Spritetm/esp32c3-doom-bauble/case/images/8a0a2fa01a11a490eb8f598237e40b69.png

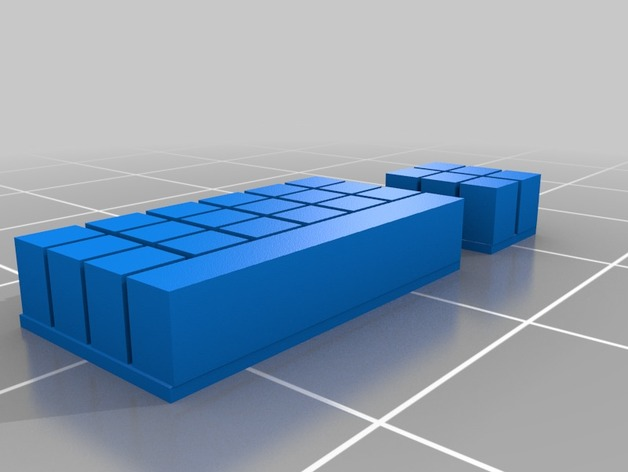
case/images/8a0a2fa01a11a490eb8f598237e40b69.png
