Spritetm/esp32c3-doom-bauble/case/images/58c1f62a23a4da21758beb00cb33d7fe.png

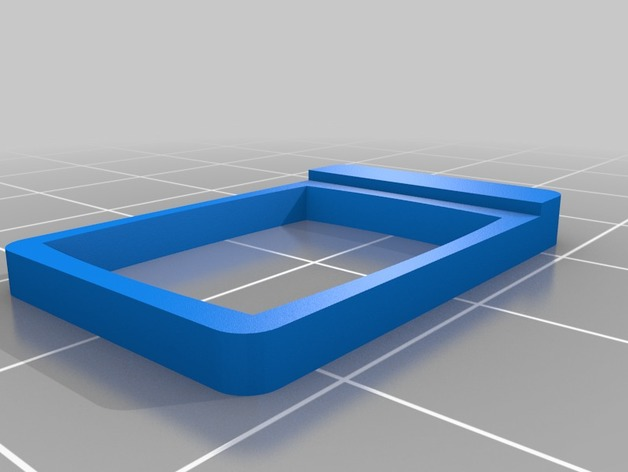
case/images/58c1f62a23a4da21758beb00cb33d7fe.png
