Spritetm/esp32c3-doom-bauble/case/images/657a22aeada5b2b08f759854bf49b2c7.png

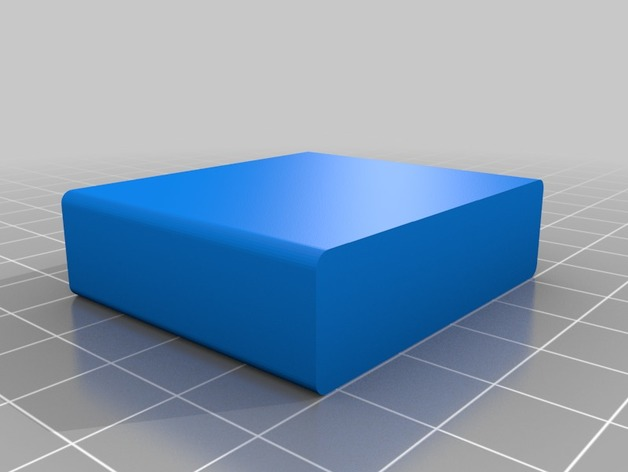
case/images/657a22aeada5b2b08f759854bf49b2c7.png
