Spritetm/esp32c3-doom-bauble/case/images/e2cab330a377aed4025e782568884b1f.png

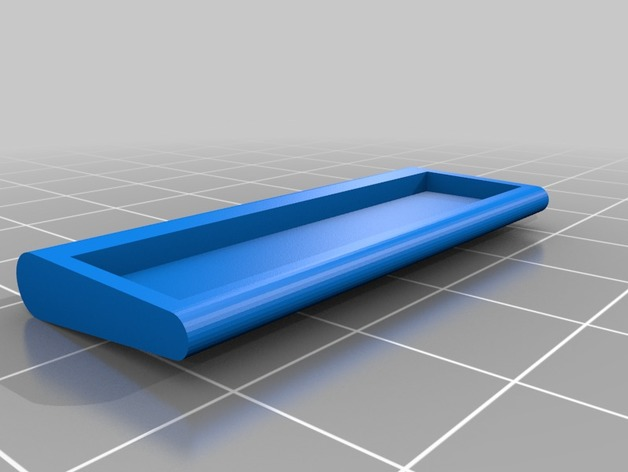
case/images/e2cab330a377aed4025e782568884b1f.png
