Spritetm/esp32c3-doom-bauble/case/images/pc3.jpg

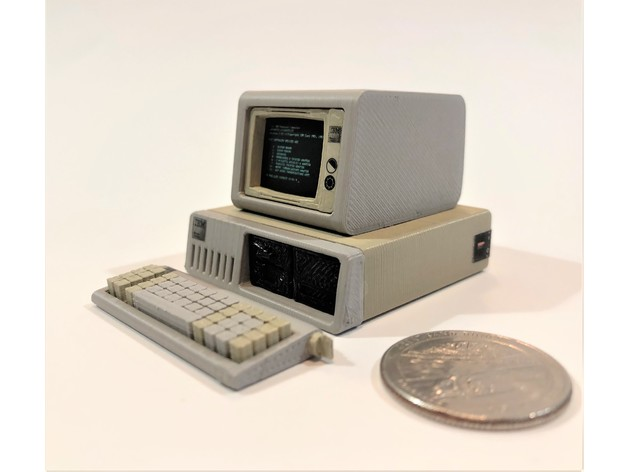
case/images/pc3.jpg
