Spritetm/esp32c3-doom-bauble/esp32c3-doom/main/s_sound.c

/* Emacs style mode select   -*- C++ -*-
 *-----------------------------------------------------------------------------
 *
 *
 *  PrBoom: a Doom port merged with LxDoom and LSDLDoom
 *  based on BOOM, a modified and improved DOOM engine
 *  Copyright (C) 1999 by
 *  id Software, Chi Hoang, Lee Killough, Jim Flynn, Rand Phares, Ty Halderman
 *  Copyright (C) 1999-2000 by
 *  Jess Haas, Nicolas Kalkhof, Colin Phipps, Florian Schulze
 *  Copyright 2005, 2006 by
 *  Florian Schulze, Colin Phipps, Neil Stevens, Andrey Budko
 *
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
 * DESCRIPTION:  Platform-independent sound code
 *
 *-----------------------------------------------------------------------------*/

// killough 3/7/98: modified to allow arbitrary listeners in spy mode
// killough 5/2/98: reindented, removed useless code, beautified

#ifdef HAVE_CONFIG_H
#include "config.h"
#endif

#include "doomstat.h"
#include "s_sound.h"
#include "i_sound.h"
#include "i_system.h"
#include "d_main.h"
#include "r_main.h"
#include "m_random.h"
#include "w_wad.h"
#include "lprintf.h"

#include "global_data.h"

// when to clip out sounds
// Does not fit the large outdoor areas.
#define S_CLIPPING_DIST (1200<<FRACBITS)

// Distance tp origin when sounds should be maxed out.
// This should relate to movement clipping resolution
// (see BLOCKMAP handling).
// Originally: (200*0x10000).

#define S_CLOSE_DIST (160<<FRACBITS)
#define S_ATTENUATOR ((S_CLIPPING_DIST-S_CLOSE_DIST)>>FRACBITS)

// Adjustable by menu.
#define NORM_PRIORITY 64
#define NORM_SEP      128

#define S_STEREO_SWING		(96*0x10000)



// number of channels available
static const unsigned int numChannels = 8;

//
// Internals.
//

void S_StopChannel(int cnum);

int S_AdjustSoundParams(mobj_t *listener, mobj_t *source, int *vol, int *sep);

static int S_getChannel(void *origin, const sfxinfo_t *sfxinfo, int is_pickup);

// Initializes sound stuff, including volume
// Sets channels, SFX and music volume,
//  allocates channel buffer, sets S_sfx lookup.
//

void S_Init(int sfxVolume, int musicVolume)
{
    //jff 1/22/98 skip sound init if sound not enabled
    if (!nosfxparm)
    {
        int i;

        lprintf(LO_CONFIRM, "S_Init: default sfx volume %d", sfxVolume);

        S_SetSfxVolume(sfxVolume);

        // Allocating the internal channels for mixing
        // (the maximum numer of sounds rendered
        // simultaneously) within zone memory.
        // CPhipps - calloc
        _g->channels =
                (channel_t *) calloc(numChannels,sizeof(channel_t));
    }

    // CPhipps - music init reformatted
    if (!nomusicparm) {
        S_SetMusicVolume(musicVolume);

        // no sounds are playing, and they are not mus_paused
        _g->mus_paused = 0;
    }
}

void S_Stop(void)
{
    unsigned int cnum;

    //jff 1/22/98 skip sound init if sound not enabled
    if (!nosfxparm)
        for (cnum=0 ; cnum<numChannels ; cnum++)
            if (_g->channels[cnum].sfxinfo)
                S_StopChannel(cnum);
}

//
// Per level startup code.
// Kills playing sounds at start of level,
//  determines music if any, changes music.
//
void S_Start(void)
{
    int mnum;

    // kill all playing sounds at start of level
    //  (trust me - a good idea)

    S_Stop();

    //jff 1/22/98 return if music is not enabled
    if (nomusicparm)
        return;

    // start new music for the level
    _g->mus_paused = 0;

    if (_g->idmusnum!=-1)
        mnum = _g->idmusnum; //jff 3/17/98 reload IDMUS music if not -1
    else
        if (_g->gamemode == commercial)
            mnum = mus_runnin + _g->gamemap - 1;
        else
        {
            static const int spmus[] =     // Song - Who? - Where?
            {
                    mus_e3m4,     // American     e4m1
                    mus_e3m2,     // Romero       e4m2
                    mus_e3m3,     // Shawn        e4m3
                    mus_e1m5,     // American     e4m4
                    mus_e2m7,     // Tim  e4m5
                    mus_e2m4,     // Romero       e4m6
                    mus_e2m6,     // J.Anderson   e4m7 CHIRON.WAD
                    mus_e2m5,     // Shawn        e4m8
                    mus_e1m9      // Tim          e4m9
        };

            if (_g->gameepisode < 4)
                mnum = mus_e1m1 + (_g->gameepisode-1)*9 + _g->gamemap-1;
            else
                mnum = spmus[_g->gamemap-1];
        }
    S_ChangeMusic(mnum, true);
}

void S_StartSoundAtVolume(mobj_t *origin, int sfx_id, int volume)
{
    int priority, cnum, is_pickup;
    const sfxinfo_t *sfx;

    int sep = NORM_SEP;

    //jff 1/22/98 return if sound is not enabled
    if (nosfxparm)
        return;

    is_pickup = sfx_id & PICKUP_SOUND || sfx_id == sfx_oof || (sfx_id == sfx_noway); // killough 4/25/98
    sfx_id &= ~PICKUP_SOUND;

    // check for bogus sound #
    if (sfx_id < 1 || sfx_id > NUMSFX)
        I_Error("S_StartSoundAtVolume: Bad sfx #: %d", sfx_id);

    sfx = &S_sfx[sfx_id];

    // Initialize sound parameters
    if (sfx->link)
    {
        priority = sfx->priority;
        volume += sfx->volume;

        if (volume < 1)
            return;

        if (volume > _g->snd_SfxVolume)
            volume = _g->snd_SfxVolume;
    }
    else
    {
        priority = NORM_PRIORITY;
    }

    // Check to see if it is audible, modify the params
    // killough 3/7/98, 4/25/98: code rearranged slightly

    if (!origin || origin == _g->player.mo)
    {
        volume *= 8;
    }
    else
        if (!S_AdjustSoundParams(_g->player.mo, origin, &volume, &sep))
            return;

    // kill old sound
    for (cnum=0 ; cnum<numChannels ; cnum++)
        if (_g->channels[cnum].sfxinfo && _g->channels[cnum].origin == origin &&
                (_g->channels[cnum].is_pickup == is_pickup))
        {
            S_StopChannel(cnum);
            break;
        }

    // try to find a channel
    cnum = S_getChannel(origin, sfx, is_pickup);

    if (cnum<0)
        return;

    int h = I_StartSound(sfx_id, cnum, volume, sep);
    if (h != -1)
    {
        _g->channels[cnum].handle = h;
        _g->channels[cnum].tickend = (_g->gametic + sfx->ticks);
    }

}

void S_StartSound(mobj_t *origin, int sfx_id)
{
    S_StartSoundAtVolume(origin, sfx_id, _g->snd_SfxVolume);
}

void S_StartSound2(degenmobj_t* origin, int sfx_id)
{
    //Look at this mess.

    //Originally, the degenmobj_t had
    //a thinker_t at the start of the struct
    //so that it could be passed around and
    //cast to a mobj_t* in the sound code
    //for non-mobj sound makers like doors.

    //This also meant that each and every sector_t
    //struct has 24 bytes wasted. I can't afford
    //to waste memory like that so we have a seperate
    //function for these cases which cobbles toget a temp
    //mobj_t-like struct to pass to the sound code.


    struct fake_mobj
    {
        thinker_t ununsed;
        degenmobj_t origin;
    } fm;

    fm.origin.x = origin->x;
    fm.origin.y = origin->y;

    S_StartSoundAtVolume((mobj_t*) &fm, sfx_id, _g->snd_SfxVolume);
}

void S_StopSound(void *origin)
{
    int cnum;

    //jff 1/22/98 return if sound is not enabled
    if (nosfxparm)
        return;

    for (cnum=0 ; cnum<numChannels ; cnum++)
        if (_g->channels[cnum].sfxinfo && _g->channels[cnum].origin == origin)
        {
            S_StopChannel(cnum);
            break;
        }
}


//
// Stop and resume music, during game PAUSE.
//
void S_PauseSound(void)
{
    //jff 1/22/98 return if music is not enabled
    if (nomusicparm)
        return;

    if (_g->mus_playing && !_g->mus_paused)
    {
        I_PauseSong(0);
        _g->mus_paused = true;
    }
}

void S_ResumeSound(void)
{
    //jff 1/22/98 return if music is not enabled
    if (nomusicparm)
        return;

    if (_g->mus_playing && _g->mus_paused)
    {
        I_ResumeSong(0);
        _g->mus_paused = false;
    }
}

static boolean S_SoundIsPlaying(int cnum)
{
    const channel_t* channel = &_g->channels[cnum];

    if(channel->sfxinfo)
    {
        int ticknow = _g->gametic;

        return (channel->tickend < ticknow);
    }

    return false;
}

//
// Updates music & sounds
//
void S_UpdateSounds(void* listener_p)
{
	mobj_t *listener = (mobj_t*) listener_p;
	int cnum;
    int sep = NORM_SEP;
	
	//jff 1/22/98 return if sound is not enabled
	if (nosfxparm)
		return;
	
	for (cnum=0 ; cnum<numChannels ; cnum++)
	{
        const sfxinfo_t *sfx;
        channel_t *c = &_g->channels[cnum];
		
		if ((sfx = c->sfxinfo))
		{
            if (S_SoundIsPlaying(c->handle))
			{
				// initialize parameters
                int volume = _g->snd_SfxVolume;

				if (sfx->link)
				{
					volume += sfx->volume;
					
					if (volume < 1)
					{
						S_StopChannel(cnum);
						continue;
					}
					else
					{
                        if (volume > _g->snd_SfxVolume)
                            volume = _g->snd_SfxVolume;

					}
				}
			}
			else   // if channel is allocated but sound has stopped, free it
				S_StopChannel(cnum);
		}
	}
}

void S_SetMusicVolume(int volume)
{
    //jff 1/22/98 return if music is not enabled
    if (nomusicparm)
        return;
    if (volume < 0 || volume > 15)
        I_Error("S_SetMusicVolume: Attempt to set music volume at %d", volume);
    I_SetMusicVolume(volume);
    _g->snd_MusicVolume = volume;
}



void S_SetSfxVolume(int volume)
{
    //jff 1/22/98 return if sound is not enabled
    if (nosfxparm)
        return;
    if (volume < 0 || volume > 127)
        I_Error("S_SetSfxVolume: Attempt to set sfx volume at %d", volume);
    _g->snd_SfxVolume = volume;
}



// Starts some music with the music id found in sounds.h.
//
void S_StartMusic(int m_id)
{
    //jff 1/22/98 return if music is not enabled
    if (nomusicparm)
        return;
    S_ChangeMusic(m_id, false);
}

void S_ChangeMusic(int musicnum, int looping)
{
    //jff 1/22/98 return if music is not enabled
    if (nomusicparm)
        return;

    if (musicnum <= mus_None || musicnum >= NUMMUSIC)
        I_Error("S_ChangeMusic: Bad music number %d", musicnum);

    if (_g->mus_playing == musicnum)
        return;

    // shutdown old music
    S_StopMusic();

    // play it
    I_PlaySong(musicnum, looping);

    _g->mus_playing = musicnum;
}


void S_StopMusic(void)
{
    //jff 1/22/98 return if music is not enabled
    if (nomusicparm)
        return;

    if (_g->mus_playing)
    {
        if (_g->mus_paused)
            I_ResumeSong(0);

        I_StopSong(0);

        _g->mus_playing = 0;
    }
}



void S_StopChannel(int cnum)
{
    int i;
    channel_t *c = &_g->channels[cnum];

    //jff 1/22/98 return if sound is not enabled
    if (nosfxparm)
        return;

    if (c->sfxinfo)
    {
        // check to see
        //  if other channels are playing the sound
        for (i=0 ; i<numChannels ; i++)
            if (cnum != i && c->sfxinfo == _g->channels[i].sfxinfo)
                break;

        // degrade usefulness of sound data
        c->sfxinfo = 0;
        c->tickend = 0;
    }
}

//
// Changes volume, stereo-separation, and pitch variables
//  from the norm of a sound effect to be played.
// If the sound is not audible, returns a 0.
// Otherwise, modifies parameters and returns 1.
//

int S_AdjustSoundParams(mobj_t *listener, mobj_t *source, int *vol, int *sep)
{
	fixed_t adx, ady,approx_dist;

	//jff 1/22/98 return if sound is not enabled
	if (nosfxparm)
		return 0;

	
	if (!listener)
		return 0;

	// calculate the distance to sound origin
	// and clip it if necessary
	adx = D_abs(listener->x - source->x);
	ady = D_abs(listener->y - source->y);

	// From _GG1_ p.428. Appox. eucledian distance fast.
	approx_dist = adx + ady - ((adx < ady ? adx : ady)>>1);

	if (!approx_dist)  // killough 11/98: handle zero-distance as special case
	{
        *vol = _g->snd_SfxVolume;
		return *vol > 0;
	}
	
	if (approx_dist > S_CLIPPING_DIST)
		return 0;
	

    // angle of source to listener
    angle_t angle = R_PointToAngle2(listener->x, listener->y, source->x, source->y);

    if (angle <= listener->angle)
        angle += 0xffffffff;

    angle -= listener->angle;
    angle >>= ANGLETOFINESHIFT;

    // stereo separation
    *sep = 128 - (FixedMul(S_STEREO_SWING,finesine[angle])>>FRACBITS);


	// volume calculation
	if (approx_dist < S_CLOSE_DIST)
        *vol = _g->snd_SfxVolume*8;
	else
		// distance effect
        *vol = (_g->snd_SfxVolume * ((S_CLIPPING_DIST-approx_dist)>>FRACBITS) * 8) / S_ATTENUATOR;
	
	return (*vol > 0);
}

//
// S_getChannel :
//   If none available, return -1.  Otherwise channel #.
//
// killough 4/25/98: made static, added is_pickup argument

static int S_getChannel(void *origin, const sfxinfo_t *sfxinfo, int is_pickup)
{
    // channel number to use
    int cnum;
    channel_t *c;

    //jff 1/22/98 return if sound is not enabled
    if (nosfxparm)
        return -1;

    // Find an open channel
    for (cnum=0; cnum<numChannels && _g->channels[cnum].sfxinfo; cnum++)
        if (origin && _g->channels[cnum].origin == origin &&
                _g->channels[cnum].is_pickup == is_pickup)
        {
            S_StopChannel(cnum);
            break;
        }

    // None available
    if (cnum == numChannels)
    {      // Look for lower priority
        for (cnum=0 ; cnum<numChannels ; cnum++)
            if (_g->channels[cnum].sfxinfo->priority >= sfxinfo->priority)
                break;
        if (cnum == numChannels)
            return -1;                  // No lower priority.  Sorry, Charlie.
        else
            S_StopChannel(cnum);        // Otherwise, kick out lower priority.
    }

    c = &_g->channels[cnum];              // channel is decided to be cnum.
    c->sfxinfo = sfxinfo;
    c->origin = origin;
    c->is_pickup = is_pickup;         // killough 4/25/98
    return cnum;
}
