Spritetm/esp32c3-doom-bauble/esp32c3-doom/main/g_game.h

/* Emacs style mode select   -*- C++ -*-
 *-----------------------------------------------------------------------------
 *
 *
 *  PrBoom: a Doom port merged with LxDoom and LSDLDoom
 *  based on BOOM, a modified and improved DOOM engine
 *  Copyright (C) 1999 by
 *  id Software, Chi Hoang, Lee Killough, Jim Flynn, Rand Phares, Ty Halderman
 *  Copyright (C) 1999-2000 by
 *  Jess Haas, Nicolas Kalkhof, Colin Phipps, Florian Schulze
 *  Copyright 2005, 2006 by
 *  Florian Schulze, Colin Phipps, Neil Stevens, Andrey Budko
 *
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
 * DESCRIPTION: Main game control interface.
 *-----------------------------------------------------------------------------*/

#ifndef __G_GAME__
#define __G_GAME__

#include "doomdef.h"
#include "d_event.h"
#include "d_ticcmd.h"

//
// GAME
//

// killough 5/2/98: number of bytes reserved for saving options
#define GAME_OPTION_SIZE 64

boolean G_Responder(event_t *ev);
boolean G_CheckDemoStatus(void);
void G_InitNew(skill_t skill, int episode, int map);
void G_DeferedInitNew(skill_t skill, int episode, int map);
void G_DeferedPlayDemo(const char *demo); // CPhipps - const
void G_LoadGame(int slot, boolean is_command); // killough 5/15/98
void G_ForcedLoadGame(void);           // killough 5/15/98: forced loadgames
void G_DoLoadGame(void);
void G_SaveGame(int slot, const char *description); // Called by M_Responder.
void G_ExitLevel(void);
void G_SecretExitLevel(void);
void G_WorldDone(void);
void G_EndGame(void); /* cph - make m_menu.c call a G_* function for this */
void G_Ticker(void);
void G_ReloadDefaults(void);     // killough 3/1/98: loads game defaults
void G_DoNewGame(void);
void G_DoReborn(int playernum);
void G_DoPlayDemo(void);
void G_DoCompleted(void);
void G_ReadDemoTiccmd(ticcmd_t *cmd);
void G_DoWorldDone(void);
void G_Compatibility(void);
const byte *G_ReadOptions(const byte *demo_p);   /* killough 3/1/98 - cph: const byte* */
void G_PlayerReborn(int player);
void G_RestartLevel(void); // CPhipps - menu involked level restart
void G_DoVictory(void);
void G_BuildTiccmd (ticcmd_t* cmd); // CPhipps - move decl to header
void G_MakeSpecialEvent(buttoncode_t bc, ...); /* cph - new event stuff */
void G_RecordDemo (const char* name);
void G_BeginRecording (void);

void G_UpdateSaveGameStrings();

void G_LoadSettings();
void G_SaveSettings();


// killough 5/2/98: moved from m_misc.c:

extern const int  key_right;
extern const int  key_left;
extern const int  key_up;
extern const int  key_down;
extern const int  key_menu_right;                                  // phares 3/7/98
extern const int  key_menu_left;                                   //     |
extern const int  key_menu_up;                                     //     V
extern const int  key_menu_down;
extern const int  key_menu_escape;                                 //     |
extern const int  key_menu_enter;                                  // phares 3/7/98
extern const int  key_strafeleft;
extern const int  key_straferight;
extern const int  key_fire;
extern const int  key_use;
extern const int  key_strafe;
extern const int  key_speed;
extern const int  key_escape;                                             // phares
extern const int  key_savegame;                                           //    |
extern const int  key_loadgame;                                           //    V
extern const int  key_reverse;
extern const int  key_zoomin;
extern const int  key_zoomout;
extern const int  key_chat;
extern const int  key_backspace;
extern const int  key_enter;
extern const int  key_help;
extern const int  key_soundvolume;
extern const int  key_hud;
extern const int  key_quicksave;
extern const int  key_endgame;
extern const int  key_messages;
extern const int  key_quickload;
extern const int  key_quit;
extern const int  key_gamma;
extern const int  key_spy;
extern const int  key_pause;
extern const int  key_setup;
extern const int  key_forward;
extern const int  key_leftturn;
extern const int  key_rightturn;
extern const int  key_backward;
extern const int  key_map_right;
extern const int  key_map_left;
extern const int  key_map_up;
extern const int  key_map_down;
extern const int  key_map_zoomin;
extern const int  key_map_zoomout;
extern const int  key_map;
extern const int  key_map_gobig;
extern const int  key_map_follow;
extern const int  key_map_mark;                                           //    ^
extern const int  key_map_clear;                                          //    |
extern const int  key_map_grid;                                           // phares


// killough 5/2/98: moved from d_deh.c:
// Par times (new item with BOOM) - from g_game.c
extern const int pars[4][10];  // hardcoded array size
extern const int cpars[32];    // hardcoded array size
// CPhipps - Make savedesciption visible in wider scope
#define SAVEDESCLEN 8

#define NUMKEYS   16


#endif
