Spritetm/esp32c3-doom-bauble/esp32c3-doom/main/i_video.c

/* Emacs style mode select   -*- C++ -*-
 *-----------------------------------------------------------------------------
 *
 *
 *  PrBoom: a Doom port merged with LxDoom and LSDLDoom
 *  based on BOOM, a modified and improved DOOM engine
 *  Copyright (C) 1999 by
 *  id Software, Chi Hoang, Lee Killough, Jim Flynn, Rand Phares, Ty Halderman
 *  Copyright (C) 1999-2006 by
 *  Jess Haas, Nicolas Kalkhof, Colin Phipps, Florian Schulze
 *  Copyright 2005, 2006 by
 *  Florian Schulze, Colin Phipps, Neil Stevens, Andrey Budko
 *
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
 * DESCRIPTION:
 *  DOOM graphics stuff for SDL
 *
 *-----------------------------------------------------------------------------
 */
#include <stdint.h>

#ifdef HAVE_CONFIG_H
#include "config.h"
#endif

#include <stdlib.h>

#ifdef HAVE_UNISTD_H
#include <unistd.h>
#endif

#include <math.h>

#include "doomstat.h"
#include "doomdef.h"
#include "doomtype.h"
#include "v_video.h"
#include "r_draw.h"
#include "d_main.h"
#include "d_event.h"
#include "i_video.h"
#include "i_system.h"
#include "i_sound.h"
#include "z_zone.h"
#include "s_sound.h"
#include "sounds.h"
#include "w_wad.h"
#include "st_stuff.h"
#include "lprintf.h"
#include "lcd.h"

#include "global_data.h"


//
// I_StartTic
//

void I_StartTic (void)
{
    I_ProcessKeyEvents();
}

//
// I_StartFrame
//
void I_StartFrame (void)
{

}

static uint8_t* fb;
static uint16_t frontpal[256];

boolean I_StartDisplay(void)
{
    _g->screens[0].data = fb;

    // Same with base row offset.
    drawvars.byte_topleft = fb;

    return true;
}

#define NO_PALETTE_CHANGE 1000



void I_EndDisplay(void) {
#if 0
//bad ascii art (as it doesn't take into account palette)
	printf("\033[1;1H");
	for (int y=0; y<SCREENHEIGHT; y+=5) {
		for (int x=0; x<SCREENWIDTH; x+=1) {
			unsigned short c=fb[x+y*SCREENWIDTH];
			int i=((c&31)*5)/32;
			if (i==0) printf(" ");
			if (i==1) printf("░");
			if (i==2) printf("▒");
			if (i==3) printf("▓");
			if (i==4) printf("█");
		}
		printf("\n");
	}
#else

//    if (_g->newpal != NO_PALETTE_CHANGE) {
		if(!_g->pallete_lump) {
			_g->pallete_lump = W_CacheLumpName("PLAYPAL");
		}
		_g->current_pallete = &_g->pallete_lump[_g->newpal*256*3];
		lcd_set_pal(_g->current_pallete);
//		_g->newpal = NO_PALETTE_CHANGE;
//	}
	lcd_render_fb(fb);
#endif
}


//
// I_InitInputs
//

static void I_InitInputs(void)
{

}
/////////////////////////////////////////////////////////////////////////////


///////////////////////////////////////////////////////////
// Palette stuff.
//
static void I_UploadNewPalette(int pal)
{
  // This is used to replace the current 256 colour cmap with a new one
  // Used by 256 colour PseudoColor modes
  
    if(!_g->pallete_lump)
    {
        _g->pallete_lump = W_CacheLumpName("PLAYPAL");
    }

    _g->current_pallete = &_g->pallete_lump[pal*256*3];
}

//////////////////////////////////////////////////////////////////////////////
// Graphics API

void I_ShutdownGraphics(void)
{
}

//
// I_UpdateNoBlit
//
void I_UpdateNoBlit (void)
{
}

//
// I_FinishUpdate
//
void I_FinishUpdate (void) {
}

//
// I_SetPalette
//
void I_SetPalette (int pal) {
    _g->newpal = pal;
}


void I_PreInitGraphics(void) {
	if (fb==NULL) fb = malloc(SCREENHEIGHT*SCREENWIDTH*2);
	assert(fb);
	lcd_init();
}

// CPhipps -
// I_SetRes
// Sets the screen resolution
void I_SetRes(void)
{
    //backbuffer
    _g->screens[0].width = SCREENWIDTH;
    _g->screens[0].height = SCREENHEIGHT;

    lprintf(LO_INFO,"I_SetRes: Using resolution %dx%d", SCREENWIDTH, SCREENHEIGHT);
}

void I_InitGraphics(void)
{
    static int    firsttime=1;

    if (firsttime)
    {
        firsttime = 0;

        lprintf(LO_INFO, "I_InitGraphics: %dx%d", SCREENWIDTH, SCREENHEIGHT);

        /* Set the video mode */
        I_UpdateVideoMode();

        /* Initialize the input system */
        I_InitInputs();

    }
}

void I_UpdateVideoMode(void)
{
  lprintf(LO_INFO, "I_SetRes: %dx%d", SCREENWIDTH, SCREENHEIGHT);
  I_SetRes();

  lprintf(LO_INFO, "R_InitBuffer:");
  R_InitBuffer();
}
