Spritetm/esp32c3-doom-bauble/esp32c3-doom/main/m_fixed.h

/* Emacs style mode select   -*- C++ -*-
 *-----------------------------------------------------------------------------
 *
 *
 *  PrBoom: a Doom port merged with LxDoom and LSDLDoom
 *  based on BOOM, a modified and improved DOOM engine
 *  Copyright (C) 1999 by
 *  id Software, Chi Hoang, Lee Killough, Jim Flynn, Rand Phares, Ty Halderman
 *  Copyright (C) 1999-2000 by
 *  Jess Haas, Nicolas Kalkhof, Colin Phipps, Florian Schulze
 *  Copyright 2005, 2006 by
 *  Florian Schulze, Colin Phipps, Neil Stevens, Andrey Budko
 *
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
 * DESCRIPTION:
 *      Fixed point arithemtics, implementation.
 *
 *-----------------------------------------------------------------------------*/

#ifndef __M_FIXED__
#define __M_FIXED__

#include "config.h"
#include "doomtype.h"

#include "m_recip.h"

/*
 * Fixed point, 32bit as 16.16.
 */

#define FRACBITS 16
#define FRACUNIT (1<<FRACBITS)


typedef int fixed_t;

/*
 * Absolute Value
 *
 * killough 5/10/98: In djgpp, use inlined assembly for performance
 * killough 9/05/98: better code seems to be gotten from using inlined C
 */

inline static int CONSTFUNC D_abs(fixed_t x)
{
  fixed_t _t = (x),_s;
  _s = _t >> (8*sizeof _t-1);
  return (_t^_s)-_s;
}

/*
 * Fixed Point Multiplication
 */

/* CPhipps - made __inline__ to inline, as specified in the gcc docs
 * Also made const */

fixed_t CONSTFUNC FixedMul(fixed_t a, fixed_t b);

/*
 * Fixed Point Division
 */

/* CPhipps - made __inline__ to inline, as specified in the gcc docs
 * Also made const */

inline static fixed_t CONSTFUNC FixedDiv(fixed_t a, fixed_t b)
{
#ifndef __arm__
    return ((unsigned)D_abs(a)>>14) >= (unsigned)D_abs(b) ? ((a^b)>>31) ^ INT_MAX :
                                                  (fixed_t)(((int_64_t) a << FRACBITS) / b);
#else

    unsigned int udiv64_arm (unsigned int a, unsigned int b, unsigned int c);

    int q;
    int sign = (a^b) < 0; /* different signs */
    unsigned int l,h;

    a = a<0 ? -a:a;
    b = b<0 ? -b:b;

    l = (a << 16);
    h = (a >> 16);

    q = udiv64_arm (h,l,b);
    if (sign)
        q = -q;

    return q;
#endif
}

/* CPhipps -
 * FixedMod - returns a % b, guaranteeing 0<=a<b
 * (notice that the C standard for % does not guarantee this)
 */

inline static fixed_t CONSTFUNC FixedMod(fixed_t a, fixed_t b)
{
    if(!a)
        return 0;

    if (b & (b-1))
    {
        fixed_t r = a % b;
        return ((r<0) ? r+b : r);
    }
    else
        return (a & (b-1));
}

//Count leading zeros. 16bit.
inline static CONSTFUNC unsigned int clz16(unsigned int x)
{
    x |= x >> 1;
    x |= x >> 2;
    x |= x >> 4;
    x |= x >> 8;

    x -= x >> 1 & 0x5555;
    x = (x >> 2 & 0x3333) + (x & 0x3333);
    x = ((x >> 4) + x) & 0x0f0f;
    x += x >> 8;

    return 16 - (x & 0x003f);
}

//Approx Reciprocal of v
inline static CONSTFUNC fixed_t FixedReciprocal(fixed_t v)
{
    fixed_t result;

    const fixed_t val = v < 0 ? -v : v;

    if(val <= (1 << FRACBITS))
    {
        result = reciprocalTable[val];
    }
    else if(val <= (2 << FRACBITS))
    {
        result = reciprocalTable[val >> 1] >> 1;
    }
    else if(val <= (4 << FRACBITS))
    {
        result = reciprocalTable[val >> 2] >> 2;
    }
    else if(val <= (8 << FRACBITS))
    {
        result = reciprocalTable[val >> 3] >> 3;
    }
    else
    {
        const unsigned int shift = 16 - clz16((val-1) >> FRACBITS);

        result = reciprocalTable[val >> shift] >> shift;
    }

    return v < 0 ? -result : result;
}


//Approx fixed point divide of a/b using reciprocal. -> a * (1/b).
inline static CONSTFUNC fixed_t FixedApproxDiv(fixed_t a, fixed_t b)
{
    return FixedMul(a, FixedReciprocal(b));
}




#endif
