Spritetm/esp32c3-doom-bauble/esp32c3-doom/main/r_draw.c

/* Emacs style mode select   -*- C++ -*-
 *-----------------------------------------------------------------------------
 *
 *
 *  PrBoom: a Doom port merged with LxDoom and LSDLDoom
 *  based on BOOM, a modified and improved DOOM engine
 *  Copyright (C) 1999 by
 *  id Software, Chi Hoang, Lee Killough, Jim Flynn, Rand Phares, Ty Halderman
 *  Copyright (C) 1999-2000 by
 *  Jess Haas, Nicolas Kalkhof, Colin Phipps, Florian Schulze
 *  Copyright 2005, 2006 by
 *  Florian Schulze, Colin Phipps, Neil Stevens, Andrey Budko
 *
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
 * DESCRIPTION:
 *      The actual span/column drawing functions.
 *      Here find the main potential for optimization,
 *       e.g. inline assembly, different algorithms.
 *
 *-----------------------------------------------------------------------------*/

#include "doomstat.h"
#include "w_wad.h"
#include "r_main.h"
#include "r_draw.h"
#include "v_video.h"
#include "st_stuff.h"
#include "g_game.h"
#include "am_map.h"
#include "lprintf.h"

#include "gba_functions.h"

#include "global_data.h"

//
// All drawing to the view buffer is accomplished in this file.
// The other refresh files only know about ccordinates,
//  not the architecture of the frame buffer.
// Conveniently, the frame buffer is a linear one,
//  and we need only the base address,
//  and the total size == width*height*depth/8.,
//


//
// Spectre/Invisibility.
//




void R_SetDefaultDrawColumnVars(draw_column_vars_t *dcvars)
{
    dcvars->x = dcvars->yl = dcvars->yh = 0;
	dcvars->iscale = dcvars->texturemid = 0;
	dcvars->source = NULL;
    dcvars->colormap = colormaps;
	dcvars->translation = NULL;
}



//
// R_DrawTranslatedColumn
// Used to draw player sprites
//  with the green colorramp mapped to others.
// Could be used with different translation
//  tables, e.g. the lighter colored version
//  of the BaronOfHell, the HellKnight, uses
//  identical sprites, kinda brightened up.
//


void R_DrawTranslatedColumn (const draw_column_vars_t *dcvars)
{
    int count = dcvars->yh - dcvars->yl;

	const byte *source = dcvars->source;
	const byte *colormap = dcvars->colormap;
	const byte *translation = dcvars->translation;

    unsigned short* dest = drawvars.byte_topleft + (dcvars->yl*SCREENPITCH) + dcvars->x;

    const fixed_t		fracstep = dcvars->iscale;
    fixed_t frac = dcvars->texturemid + (dcvars->yl - centery)*fracstep;
 
	const unsigned int sw = SCREENWIDTH;

    // Zero length, column does not exceed a pixel.
    if (count < 0)
        return;

    // Here we do an additional index re-mapping.
    do 
    {
		// Translation tables are used
		//  to map certain colorramps to other ones,
		//  used with PLAY sprites.
		// Thus the "green" ramp of the player 0 sprite
		//  is mapped to gray, red, black/indigo. 
        unsigned short color = colormap[translation[source[frac>>FRACBITS]]];

        *dest = (color | (color << 8));
		dest += sw;
	
		frac += fracstep;
    } while (count--); 
} 





//
// R_InitBuffer
// Creats lookup tables that avoid
//  multiplies and other hazzles
//  for getting the framebuffer address
//  of a pixel to draw.
//

void R_InitBuffer()
{
	// Same with base row offset.
    drawvars.byte_topleft = _g->screens[0].data;


}
