Spritetm/esp32c3-doom-bauble/esp32c3-doom/GbaWadUtil/wadprocessor.h

#ifndef WADPROCESSOR_H
#define WADPROCESSOR_H

#include <QtCore>
#include "wadfile.h"

class WadProcessor : public QObject
{
    Q_OBJECT
public:
    explicit WadProcessor(WadFile& wad, QObject *parent = nullptr);

    bool ProcessWad();

private:

    bool ProcessD2Levels();
    bool ProcessD1Levels();

    bool ProcessLevel(quint32 lumpNum);

    bool ProcessVertexes(quint32 lumpNum);
    bool ProcessLines(quint32 lumpNum);
    bool ProcessSegs(quint32 lumpNum);
    bool ProcessSides(quint32 lumpNum);

    bool ProcessPNames();
    bool RemoveUnusedLumps();
	bool ReplaceMusic();
	bool ReplaceDemos();

    int GetTextureNumForName(const char* tex_name);

    WadFile& wadFile;

};

#endif // WADPROCESSOR_H
